Webhiver/tost/src/discovery.py

import asyncio
import socket
import random
from constants import DISCOVERY_PORT
from wifi import wifi
from config import config
from state import state

DISCOVERY_JITTER_MS = 1000
DISCOVERY_POLL_MS = 20
SOCKET_RETRY_S = 30


class DiscoveryManager:
    """UDP-based device discovery for finding thermostats on the network.
    
    Socket lifecycle is driven entirely by wifi_connected state changes.
    The async loop only reads incoming messages from the socket.
    """
    
    def __init__(self):
        self._socket = None
        self._needs_open = False
        self._needs_announce = False
        state.subscribe("wifi_connected", self._on_wifi_changed)
        config.subscribe("satellites", self._on_satellites_config_change)
    
    def _on_satellites_config_change(self, new_sats, old_sats):
        if config.get("mode") != "host":
            return
        new_macs = {s.get("mac", "").lower() for s in new_sats if isinstance(s, dict)}
        old_macs = {s.get("mac", "").lower() for s in old_sats if isinstance(s, dict)}
        if new_macs - old_macs:
            self.send_discover_message()

    def _on_wifi_changed(self, connected, was_connected):
        if connected and not was_connected:
            if self._open():
                self._needs_announce = True
            else:
                self._needs_open = True
        elif not connected and was_connected:
            self._close()
            self._needs_open = False
            self._needs_announce = False
    
    def _open(self):
        """Create the non-blocking UDP socket for listening and broadcasting."""
        self._close()
        try:
            sock = socket.socket(socket.AF_INET, socket.SOCK_DGRAM)
            sock.setsockopt(socket.SOL_SOCKET, socket.SO_REUSEADDR, 1)
            sock.setsockopt(socket.SOL_SOCKET, socket.SO_BROADCAST, 1)
            sock.bind(('0.0.0.0', DISCOVERY_PORT))
            sock.setblocking(False)
            self._socket = sock
            print("Discovery: listening on port", DISCOVERY_PORT)
            return True
        except Exception as e:
            print("Discovery: socket error:", e)
            return False
    
    def _close(self):
        if self._socket:
            try:
                self._socket.close()
            except Exception:
                pass
            self._socket = None
    
    def _announce(self):
        """Send initial announcement based on device mode."""
        mode = config.get("mode", "host")
        if mode == "host":
            self.send_discover_message()
        elif mode == "satellite":
            self._broadcast_iam()

    def _broadcast(self, message):
        """Send a UDP broadcast via the listening socket."""
        if not self._socket:
            return False
        try:
            dest = wifi.broadcast_address or '255.255.255.255'
            self._socket.sendto(message.encode(), (dest, DISCOVERY_PORT))
            return dest
        except Exception as e:
            print("Discovery: broadcast failed:", e)
            return False
    
    def send_discover_message(self):
        """Broadcast a DISCOVER message on the network."""
        if not wifi.ip_address:
            return
        dest = self._broadcast("DISCOVER")
        if dest:
            print("Discovery: sent DISCOVER broadcast to", dest)
    
    def _broadcast_iam(self):
        mac = wifi.get_mac()
        if not mac:
            return
        dest = self._broadcast("IAM|{}".format(mac))
        if dest:
            print("Discovery: sent IAM broadcast to", dest)
    
    def _send_iam_to(self, addr):
        """Send IAM reply to a specific address via the listening socket."""
        mac = wifi.get_mac()
        if not mac or not self._socket:
            return
        try:
            self._socket.sendto("IAM|{}".format(mac).encode(), addr)
            print("Discovery: sent IAM to", addr[0])
        except Exception as e:
            print("Discovery: failed to send IAM to", addr[0], ":", e)
    
    async def _handle_message(self, data, addr):
        try:
            message = data.decode().strip()
            mode = config.get("mode", "host")
            
            if message == "DISCOVER" and mode == "satellite":
                print("Discovery: received DISCOVER from", addr[0])
                jitter = random.randint(0, DISCOVERY_JITTER_MS)
                await asyncio.sleep_ms(jitter)
                self._send_iam_to((addr[0], DISCOVERY_PORT))
            
            elif message.startswith("IAM|") and mode == "host":
                parts = message.split('|')
                if len(parts) >= 2:
                    mac = parts[1].lower()
                    ip = addr[0]
                    print("Discovery: received IAM from", mac, "at", ip)
                    self._update_satellite_ip(mac, ip)
        except Exception as e:
            print("Discovery: handle error:", e)
    
    def _update_satellite_ip(self, mac, ip):
        """Update the IP for a satellite in state, matched by MAC."""
        satellites = state.get("satellites", [])
        updated = []
        changed = False
        
        for sat in satellites:
            if sat.get("mac", "").lower() == mac.lower():
                if sat.get("ip") != ip:
                    sat = sat.copy()
                    sat["ip"] = ip
                    changed = True
            updated.append(sat)
        
        if changed:
            state.set("satellites", updated)
            print("Discovery: updated", mac, "->", ip)
    
    async def loop(self):
        """Listen for incoming discovery messages.
        
        Socket creation is handled by _on_wifi_changed. The loop only retries
        if the initial creation failed, and otherwise just reads messages.
        """
        while True:
            if self._needs_open and not self._socket:
                if self._open():
                    self._needs_open = False
                    self._needs_announce = True
                else:
                    print("Discovery: retry in", SOCKET_RETRY_S, "s")
                    await asyncio.sleep(SOCKET_RETRY_S)
                    continue
            
            if self._needs_announce and self._socket:
                self._announce()
                self._needs_announce = False
            
            if self._socket:
                while True:
                    try:
                        data, addr = self._socket.recvfrom(256)
                    except OSError:
                        break
                    except Exception as e:
                        print("Discovery: error:", e)
                        self._close()
                        self._needs_open = True
                        break
                    await self._handle_message(data, addr)

            await asyncio.sleep_ms(DISCOVERY_POLL_MS)


discovery = DiscoveryManager()
