Webhiver/tost/src/relay_manager.py

from time import ticks_ms
from lib.picozero import DigitalOutputDevice
import hardware_config
from state_manager import state


class RelayManager:
    
    def __init__(self):
        self._relay = DigitalOutputDevice(
            pin=hardware_config.PIN_RELAY,
            active_high=True,
            initial_value=False
        )
        
        state.subscribe("flame", self._on_flame_change)
    
    def _on_flame_change(self, new_flame, old_flame):
        if state.get("config", {}).get("mode") == "satellite":
            return
        
        if new_flame:
            self._relay.on()
            if not old_flame:
                state.set("flame_start_tick", ticks_ms())
        else:
            self._relay.off()
            state.set("flame_start_tick", None)
    
    def on(self):
        self._relay.on()
    
    def off(self):
        self._relay.off()
    
    @property
    def is_on(self):
        return self._relay.value == 1
    
    def close(self):
        self.off()
        self._relay.close()


relay = RelayManager()
